transistorfet/deskclock2/software/DeskClock2/OverpassMono14pt7b.h

const uint8_t OverpassMono14pt7bBitmaps[] PROGMEM = {
  0x00, 0x77, 0x77, 0x77, 0x76, 0x66, 0x62, 0x22, 0x07, 0xF7, 0x70, 0xE7,
  0x67, 0x63, 0x63, 0x63, 0x63, 0x63, 0x03, 0x1C, 0x07, 0x18, 0x06, 0x18,
  0x06, 0x18, 0x06, 0x18, 0x3F, 0xFF, 0x3F, 0xFF, 0x06, 0x38, 0x0E, 0x30,
  0x0C, 0x30, 0x0C, 0x30, 0x0C, 0x30, 0x7F, 0xFE, 0xFF, 0xFE, 0x0C, 0x70,
  0x1C, 0x60, 0x18, 0x60, 0x18, 0x60, 0x18, 0x60, 0x07, 0x00, 0x70, 0x0F,
  0x83, 0xFE, 0x70, 0xE6, 0x07, 0x60, 0x06, 0x00, 0x70, 0x03, 0xC0, 0x3F,
  0x00, 0xFC, 0x03, 0xE0, 0x0F, 0x00, 0x70, 0x03, 0x00, 0x36, 0x03, 0xE0,
  0x37, 0x87, 0x3F, 0xE0, 0xF8, 0x07, 0x00, 0x70, 0x3C, 0x07, 0x7E, 0x06,
  0x63, 0x0C, 0xC3, 0x18, 0xC3, 0x18, 0xC3, 0x30, 0x63, 0x60, 0x7E, 0x60,
  0x3C, 0xC0, 0x01, 0x80, 0x01, 0xBC, 0x03, 0x7E, 0x06, 0x63, 0x0E, 0xC3,
  0x0C, 0xC1, 0x18, 0xC1, 0x38, 0x63, 0x30, 0x7E, 0x60, 0x3C, 0x07, 0x80,
  0x1F, 0xE0, 0x1C, 0xE0, 0x18, 0x60, 0x18, 0x60, 0x18, 0x60, 0x1C, 0xE0,
  0x0F, 0xC0, 0x0F, 0x00, 0x1F, 0x80, 0x39, 0x8C, 0x71, 0xCC, 0x60, 0xEC,
  0xE0, 0x7C, 0xE0, 0x38, 0x60, 0x3C, 0x70, 0xFC, 0x3F, 0xCE, 0x1F, 0x07,
  0xFF, 0xED, 0xB0, 0x07, 0x0E, 0x1C, 0x18, 0x30, 0x30, 0x70, 0x60, 0x60,
  0xE0, 0xE0, 0xE0, 0xE0, 0x60, 0x60, 0x60, 0x70, 0x30, 0x38, 0x18, 0x1C,
  0x0F, 0xC0, 0xC0, 0xC0, 0xC1, 0xC1, 0x83, 0x07, 0x06, 0x0C, 0x18, 0x30,
  0x60, 0xC1, 0x87, 0x0C, 0x18, 0x61, 0xC3, 0x1C, 0x00, 0x10, 0x81, 0xC7,
  0x07, 0x70, 0x1B, 0x00, 0xF0, 0x7F, 0xFF, 0xFF, 0xE1, 0xE0, 0x1D, 0x80,
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
  {   881,  11,  19,  17,    3,  -18 },   // 0x46 'F'
  {   908,  13,  19,  17,    2,  -18 },   // 0x47 'G'
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

const GFXfont OverpassMono14pt7b PROGMEM = {
  (uint8_t  *)OverpassMono14pt7bBitmaps,
  (GFXglyph *)OverpassMono14pt7bGlyphs,
  0x20, 0x7E, 35 };

// Approx. 2977 bytes
